maxsoulard/dum.bot/trinket.py

#!/usr/bin/python
# -*- encoding: utf8 -*-

import smbus
import time

class TrinketI2C():

    def __init__(self):
        self.DEV_ADDR = 0x04
        self.bus = smbus.SMBus(1)
        self.reads = 0
        self.errs = 0
        self.vals = []
        self.av = 0

    def readvalues(self):
        # try:
            # read value from i2c (trinket)
            a_val = self.bus.read_word_data(self.DEV_ADDR, 0)
            self.vals.append(a_val)
            # print("Read value [%s]; no. of reads [%s]; no. of errors [%s]" % (a_val, reads, errs))

            return a_val

        # except Exception as ex:
            # TODO gestion exception à remonter à webdumbot
            # self.errs += 1
            # print("Exception [%s]" % (ex))
            # return 1000
            # pass
